Gaboze-Pocaio/Kickstarter/docs/assets/gameboyzero-split-board/__auto_2.png

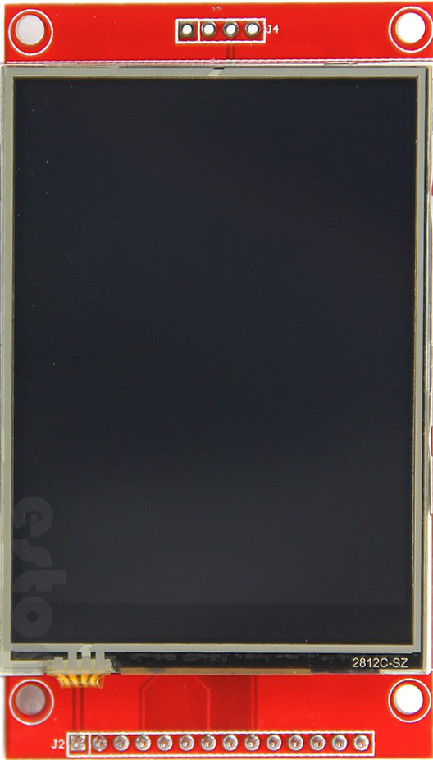
docs/assets/gameboyzero-split-board/__auto_2.png
