Gaboze-Pocaio/Kickstarter/docs/assets/gameboyzero-split-board/__auto_22.jpg

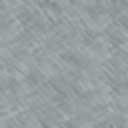
docs/assets/gameboyzero-split-board/__auto_22.jpg
