Gaboze-Pocaio/Kickstarter/docs/assets/gameboyzero-split-board/__auto_34.jpg

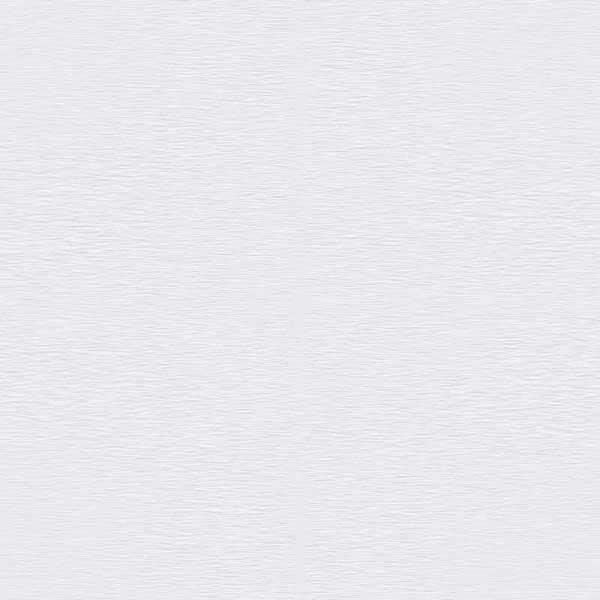
docs/assets/gameboyzero-split-board/__auto_34.jpg
