Gaboze-Pocaio/Kickstarter/docs/assets/gameboyzero-split-board/__auto_36.png

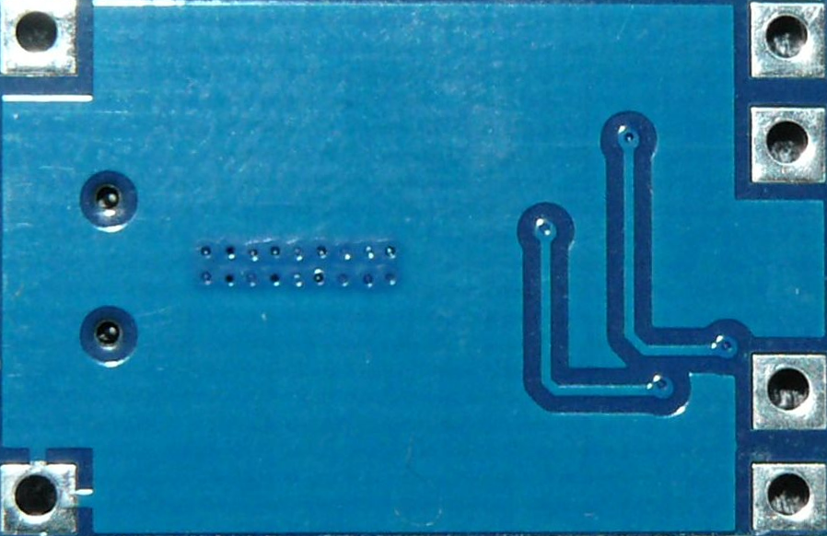
docs/assets/gameboyzero-split-board/__auto_36.png
