Gaboze-Pocaio/Kickstarter/docs/assets/gameboyzero-split-board/eagleUp_gameboyzero-split-bottom_bottom_board1.png

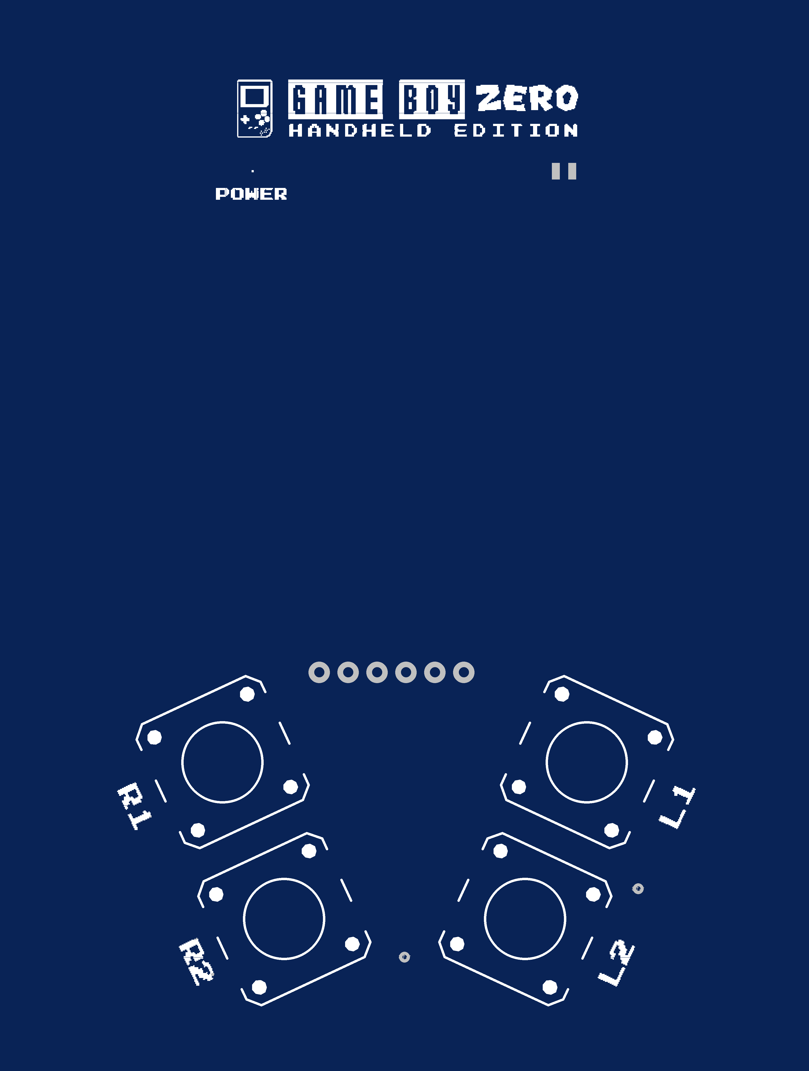
docs/assets/gameboyzero-split-board/eagleUp_gameboyzero-split-bottom_bottom_board1.png
