Gaboze-Pocaio/Kickstarter/docs/assets/gameboyzero-split-board/eagleUp_gameboyzero-split-top_top_board.png

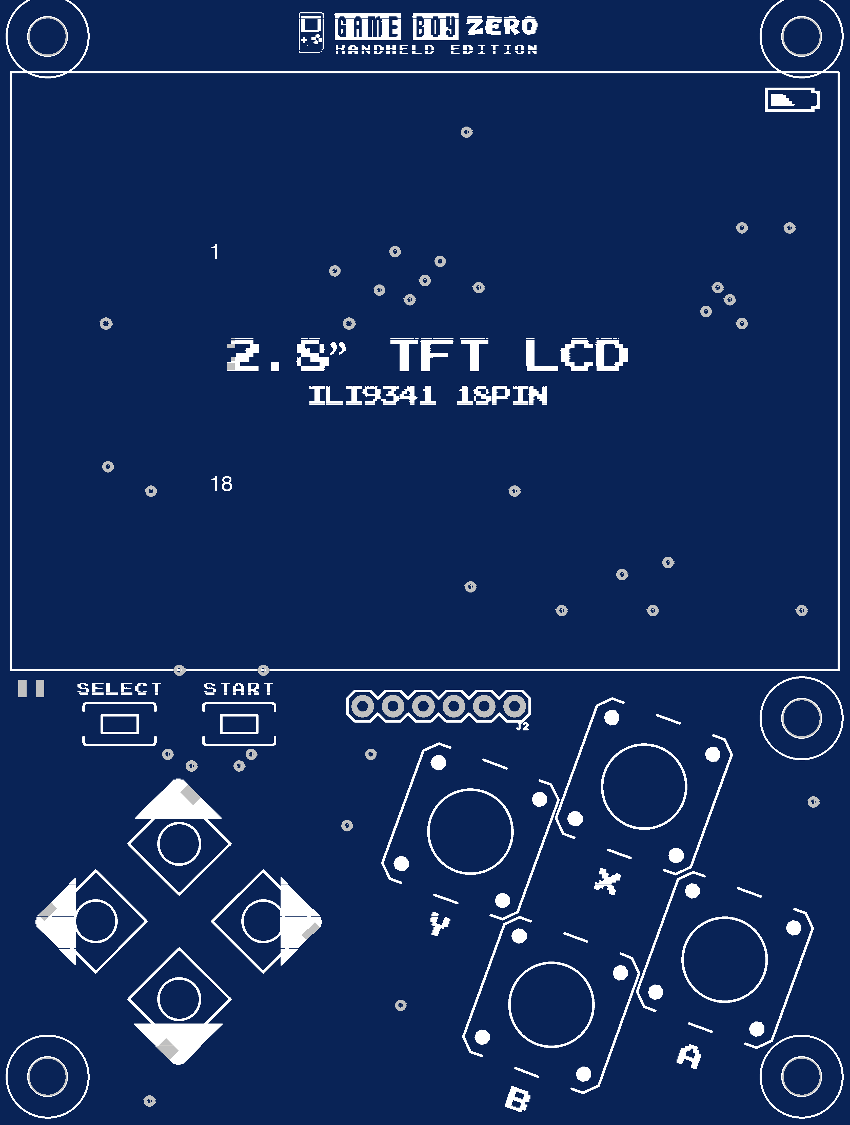
docs/assets/gameboyzero-split-board/eagleUp_gameboyzero-split-top_top_board.png
