Gaboze-Pocaio/Kickstarter/docs/assets/loader.gif

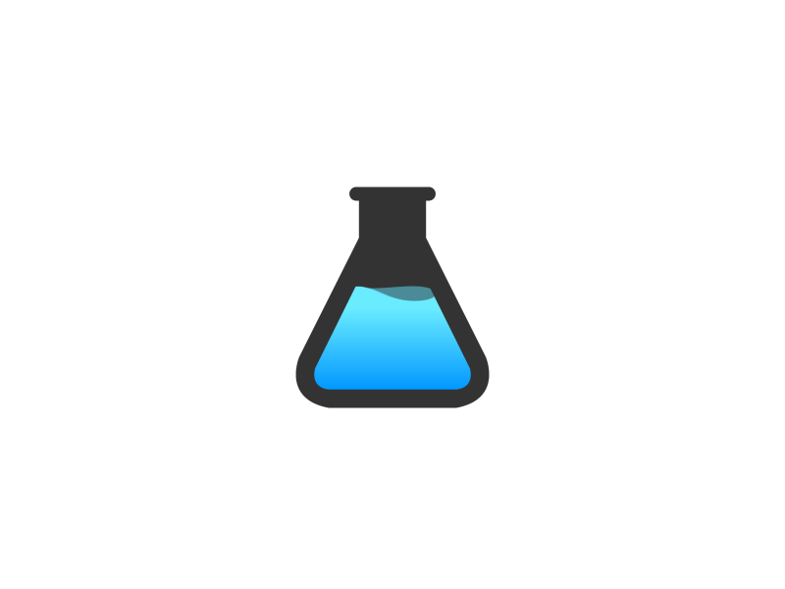
docs/assets/loader.gif
