Gaboze-Pocaio/Kickstarter/images/colors.png

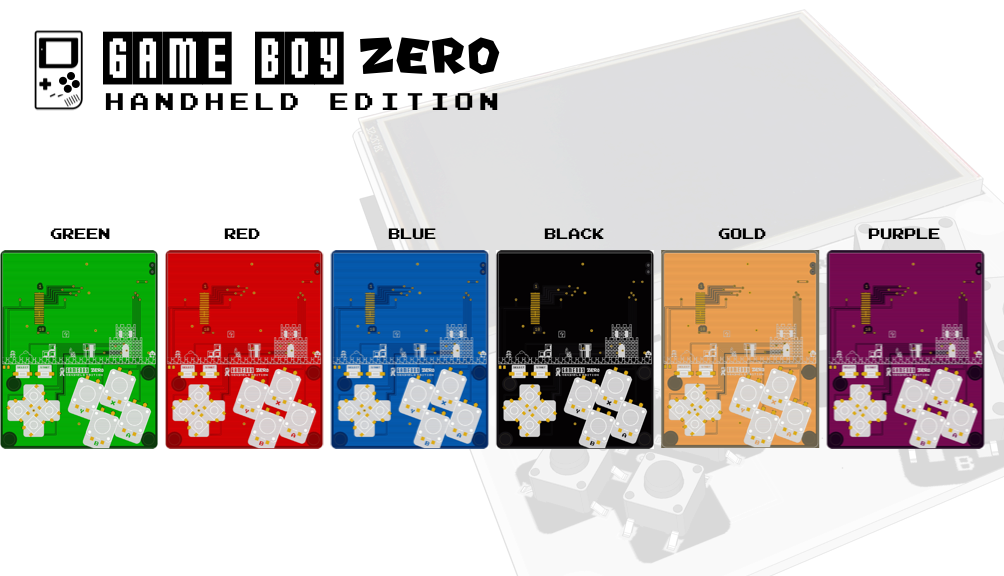
images/colors.png
