Gaboze-Pocaio/Kickstarter/images/hero.png

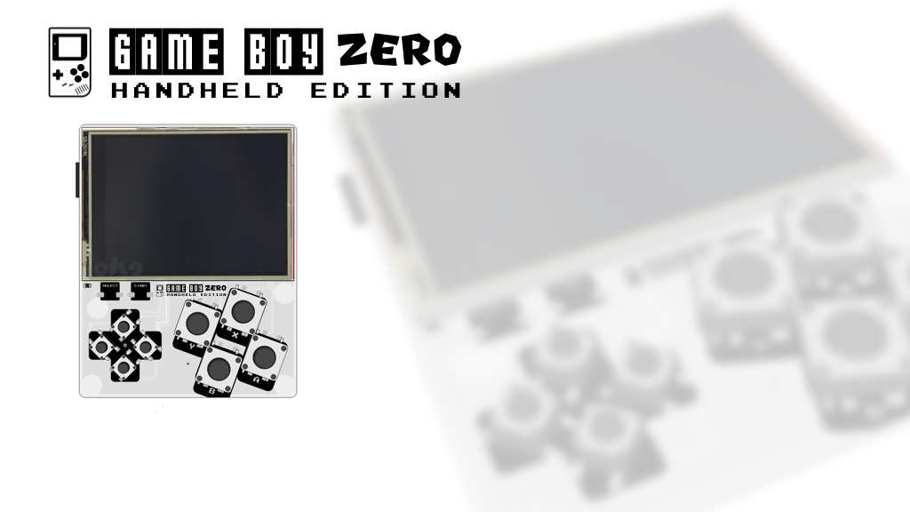
images/hero.png
