Gaboze-Pocaio/Kickstarter/images/sfctp_clear.png

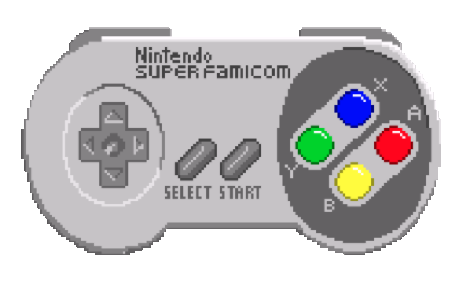
images/sfctp_clear.png
