Gaboze-Pocaio/Kickstarter/silks/gameboyzero-holiday-bottom.bmp

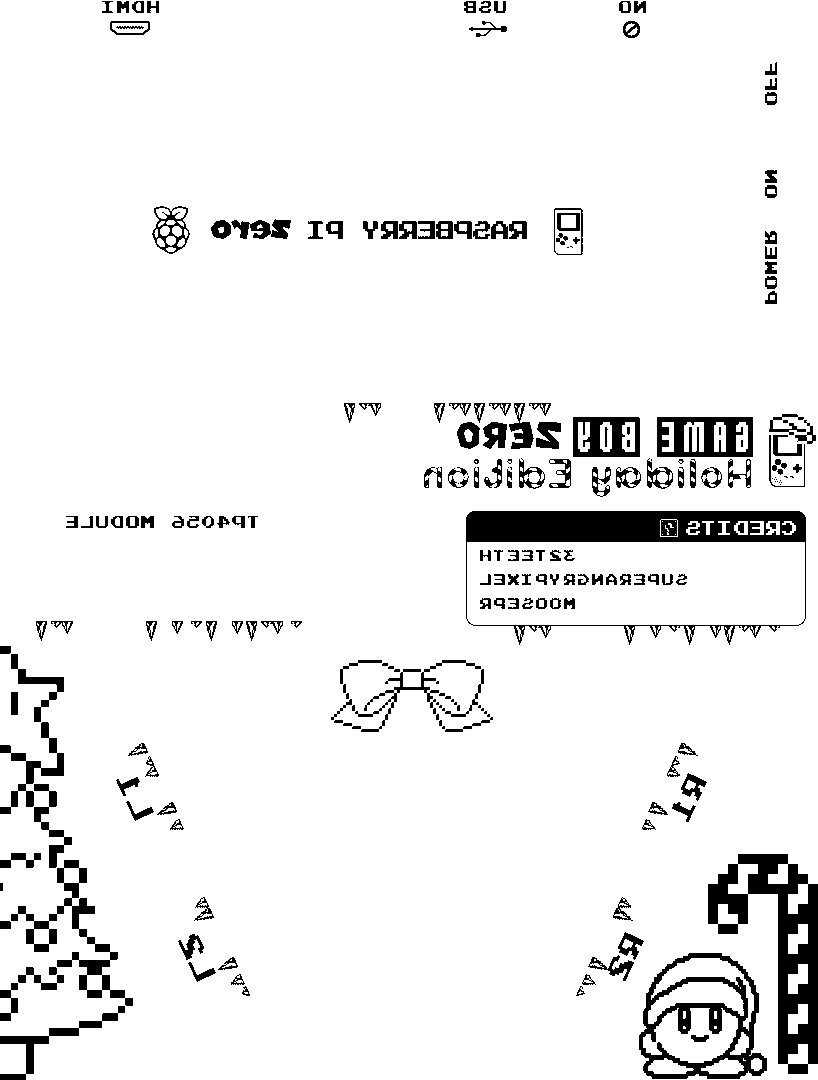
silks/gameboyzero-holiday-bottom.bmp
