Gaboze-Pocaio/Kickstarter/silks/gameboyzero-holiday-top.bmp

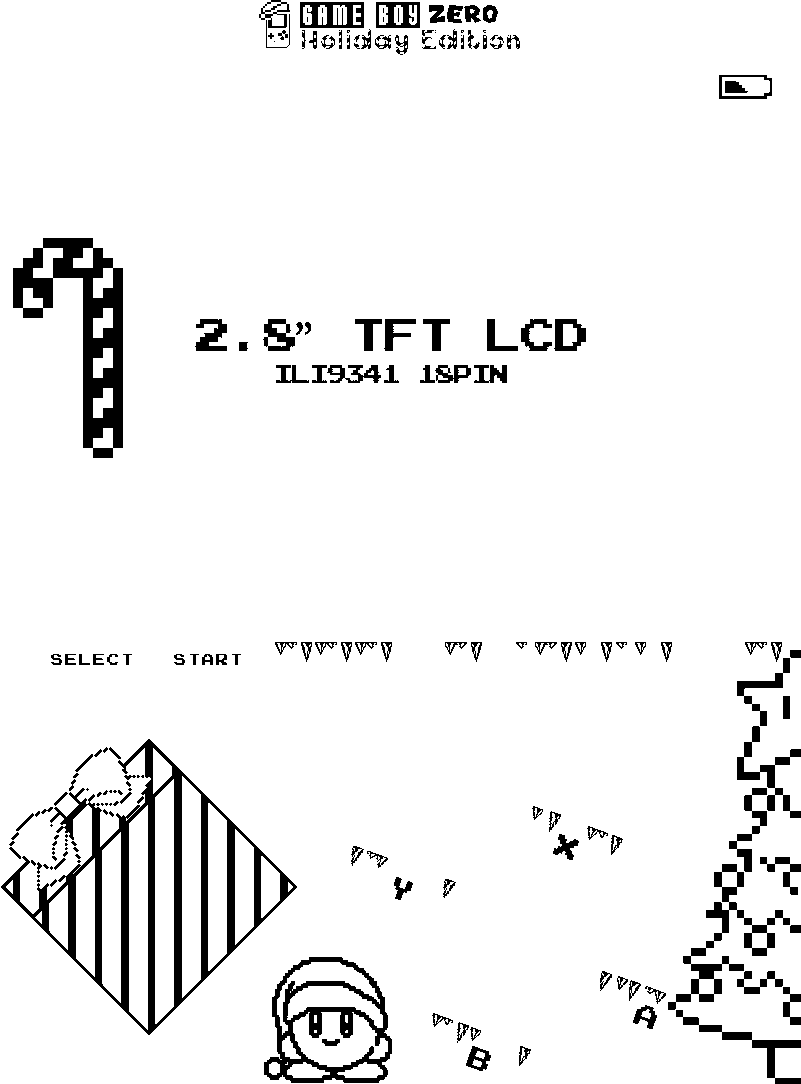
silks/gameboyzero-holiday-top.bmp
